eez-open/xmos-eval-board/BOM/EEZ XMOS eval r1B5 parts values.png

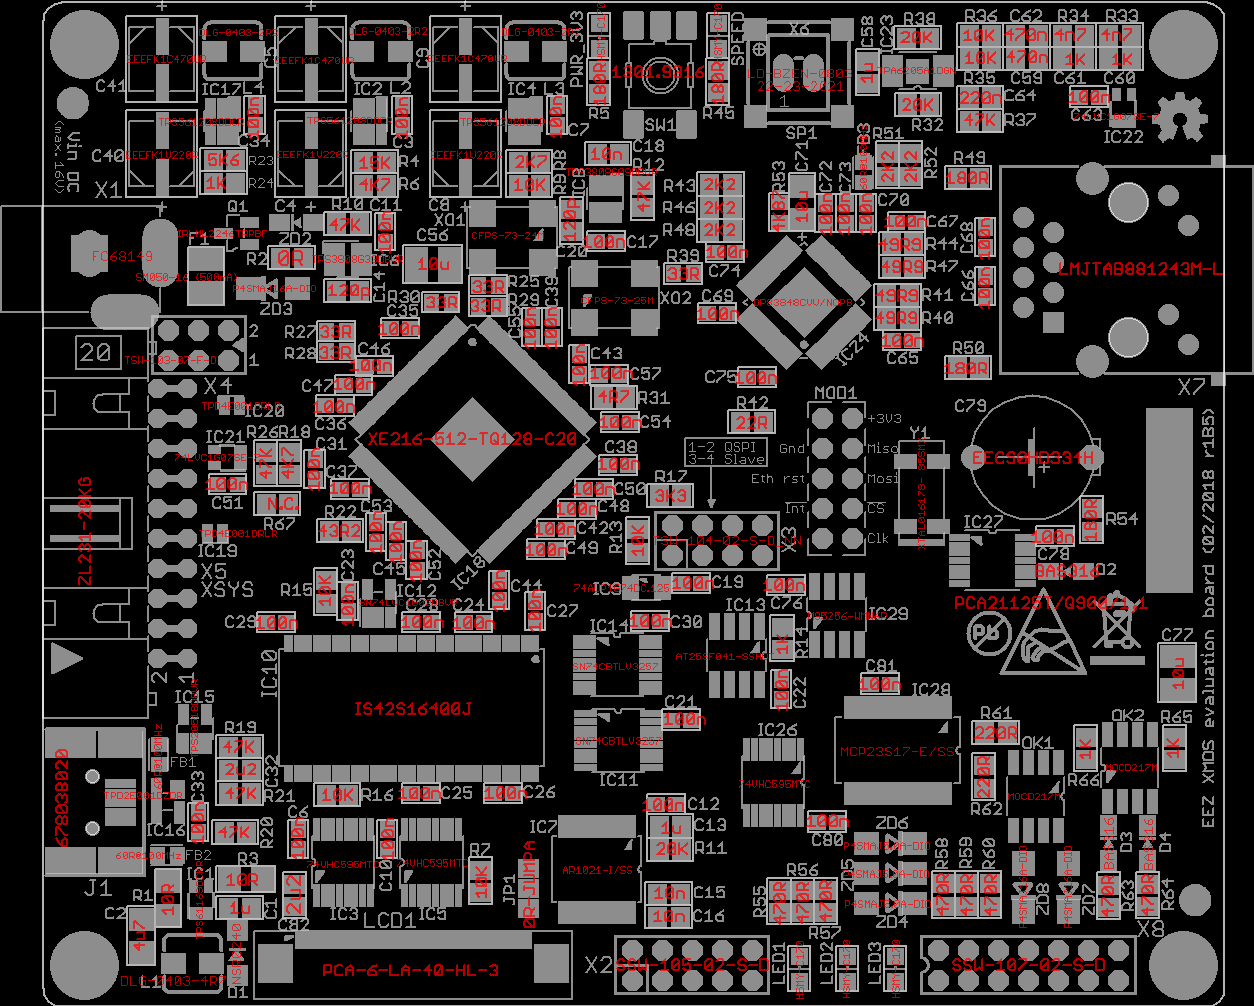
BOM/EEZ XMOS eval r1B5 parts values.png
