eez-open/xmos-eval-board/Simulation/Flash startup.asc

A2: dflop; vhigh=5 vlow=0 td=10n trise=5n
Latch: voltage; PULSE(0 5 150m 10n 10n 10m 20m)
Reset: voltage; PULSE(0 5 50m 10n 10n 50m 350m 2)
Set: voltage; 5v
Named nets: 0, MUX_S, RESET, LATCH
.tran 0 1s 0 1m
.options plotwinsize=0 ; disable data compression is optional
